michigan-balloon-recovery/ATACS/software/rtos/src/MSP430-5438STK_HAL/hal_MSP430-5438STK.h

/*******************************************************************************
    Filename: hal_MSP430-5438STK.h

This is the master header file and also the only necessary file to be included
in order to use MSP430-5438STK HAL.
***************************************************************************/
#ifndef HAL_MSP430_5438STK_H
#define HAL_MSP430_5438STK_H

#include <MSP430-5438STK_HAL/hal_board.h>
#include <MSP430-5438STK_HAL/hal_buttons.h>
#include "msp430.h"

#include "hal_UCS.h"
#include "HAL_PMM.h"

#endif /* HAL_MSP430_5438STK_H */
